Eucitzen/liam/STM32_PCB/Liam_PCB/MCU_POWER.kicad_sch

## KiCad design STM32_PCB/Liam_PCB/MCU_POWER.kicad_sch (2025-02-24)

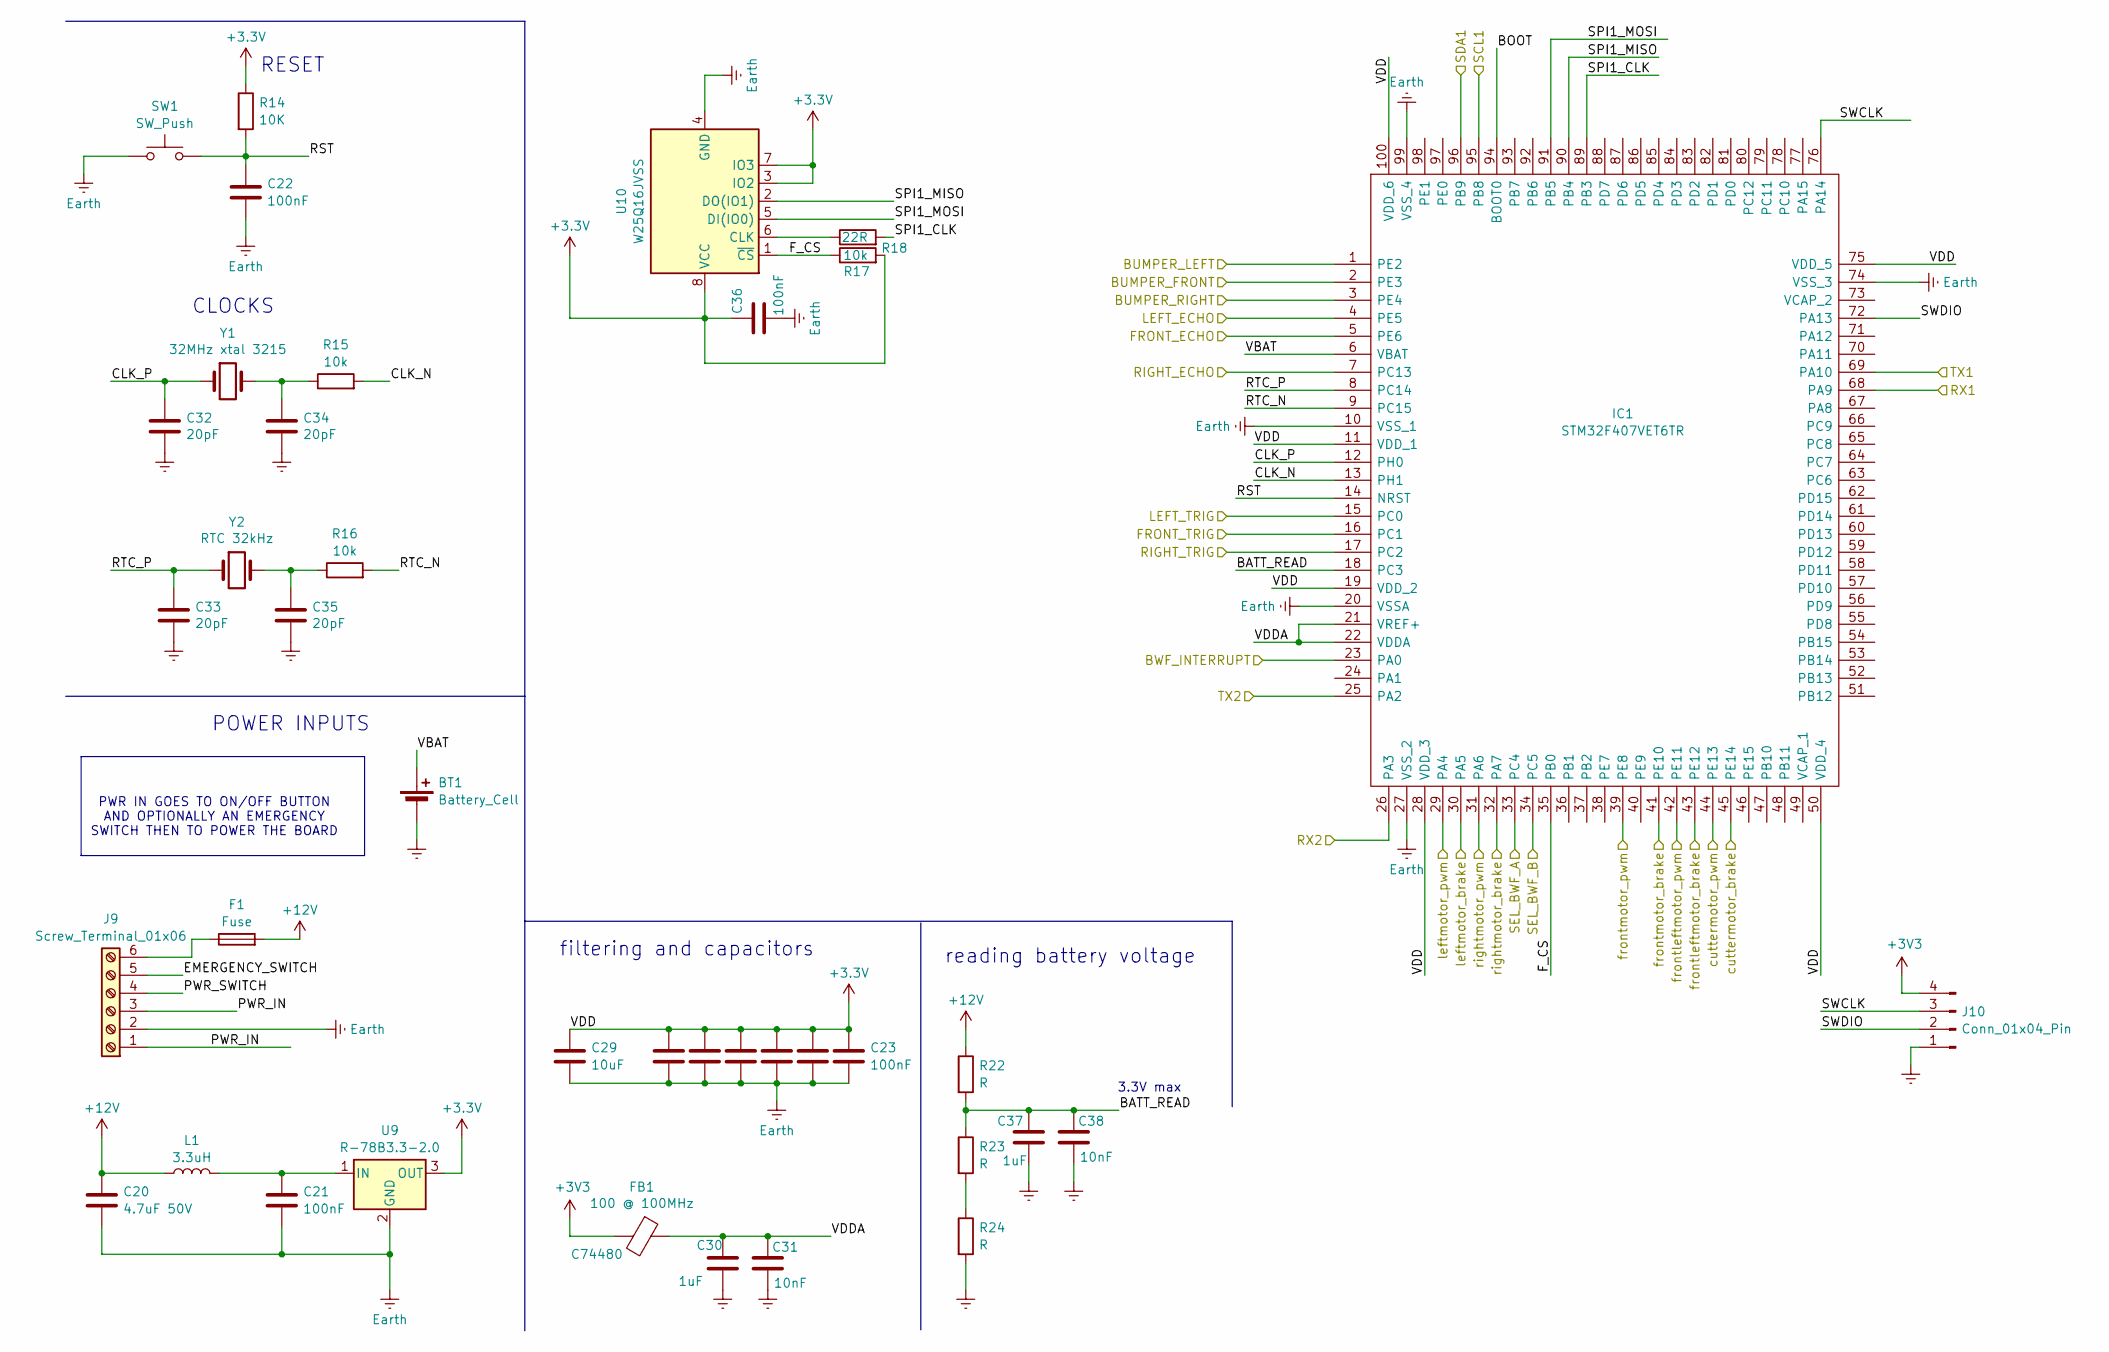
[picture p8: schematic MCU_POWER.kicad_sch]

Parts:
BT1: Battery_Cell
C20: 4.7uF 50V
C21, C22, C23, C24, C25, C26, C27, C28, C36: 100nF
C29: 10uF
C30, C37: 1uF; C_0805_2012Metric_Pad1.15x1.40mm_HandSolder
C31, C38: 10nF; C_0805_2012Metric_Pad1.15x1.40mm_HandSolder
C32, C33, C34, C35: 20pF; C_0805_2012Metric_Pad1.18x1.45mm_HandSolder
F1: Fuse
FB1: 100 @ 100MHz; L_0805_2012Metric_Pad1.15x1.40mm_HandSolder
IC1: STM32F407VET6TR; QFP50P1600X1600X160-100N; Manufacturer_Part_Number STM32F407VET6TR; Mouser Part Number 511-STM32F407VET6TR
J9: Screw_Terminal_01x06
J10: Conn_01x04_Pin
L1: 3.3uH
R14: 10K
R15, R16, R17: 10k
R18: 22R
R22, R23, R24: R
SW1: SW_Push
U9: R-78B3.3-2.0; Converter_DCDC_RECOM_R-78B-2.0_THT
U10: W25Q16JVSS; SOIC-8_5.23x5.23mm_P1.27mm
Y1: 32MHz xtal 3215; Crystal_SMD3215
Y2: RTC 32kHz; Crystal_SMD_HC49-SD_HandSoldering

Connections:
+3.3V: C23.1, C24.1, C25.1, C26.1, C27.1, C28.1, C29.1, C36.1, IC1.11 (VDD_1), IC1.19 (VDD_2), IC1.28 (VDD_3), IC1.50 (VDD_4), IC1.75 (VDD_5), IC1.100 (VDD_6), R14.1, R17.2, U9.3 (OUT), U10.3 (IO2), U10.7 (IO3), U10.8 (VCC)
+3V3: FB1.2, J10.4
+12V: C20.1, F1.2, L1.1, R22.1
BATT_READ: C37.1, C38.1, IC1.18 (PC3), R22.2, R23.1
BOOT: IC1.94 (BOOT0)
BUMPER_FRONT: IC1.2 (PE3)
BUMPER_LEFT: IC1.1 (PE2)
BUMPER_RIGHT: IC1.3 (PE4)
BWF_INTERRUPT: IC1.23 (PA0)
CLK_N: IC1.13 (PH1), R15.2
CLK_P: C32.1, IC1.12 (PH0), Y1.1
EMERGENCY_SWITCH: J9.5
Earth: BT1.2 (-), C20.2, C21.2, C22.2, C23.2, C24.2, C25.2, C26.2, C27.2, C28.2, C29.2, C30.2, C31.2, C32.2, C33.2, C34.2, C35.2, C36.2, C37.2, C38.2, IC1.10 (VSS_1), IC1.20 (VSSA), IC1.27 (VSS_2), IC1.74 (VSS_3), IC1.99 (VSS_4), J9.2, J10.1, R24.2, SW1.1, U9.2 (GND), U10.4 (GND)
FRONT_ECHO: IC1.5 (PE6)
FRONT_TRIG: IC1.16 (PC1)
F_CS: IC1.35 (PB0), R17.1, U10.1 (~CS)
LEFT_ECHO: IC1.4 (PE5)
LEFT_TRIG: IC1.15 (PC0)
unnamed: C21.1, L1.2, U9.1 (IN)
unnamed: C34.1, R15.1, Y1.2
unnamed: C35.1, R16.1, Y2.2
unnamed: F1.1, J9.6
unnamed: R18.1, U10.6 (CLK)
unnamed: R23.2, R24.1
PWR_IN: J9.1, J9.3
PWR_SWITCH: J9.4
RIGHT_ECHO: IC1.7 (PC13)
RIGHT_TRIG: IC1.17 (PC2)
RST: C22.1, IC1.14 (NRST), R14.2, SW1.2
RTC_N: IC1.9 (PC15), R16.2
RTC_P: C33.1, IC1.8 (PC14), Y2.1
RX1: IC1.68 (PA9)
RX2: IC1.26 (PA3)
SCL1: IC1.95 (PB8)
SDA1: IC1.96 (PB9)
SEL_BWF_A: IC1.33 (PC4)
SEL_BWF_B: IC1.34 (PC5)
SPI1_CLK: IC1.89 (PB3), R18.2
SPI1_MISO: IC1.90 (PB4), U10.2 (DO(IO1))
SPI1_MOSI: IC1.91 (PB5), U10.5 (DI(IO0))
SWCLK: IC1.76 (PA14), J10.3
SWDIO: IC1.72 (PA13), J10.2
TX1: IC1.69 (PA10)
TX2: IC1.25 (PA2)
VBAT: BT1.1 (+), IC1.6 (VBAT)
VDDA: C30.1, C31.1, FB1.1, IC1.21 (VREF+), IC1.22 (VDDA)
cuttermotor_brake: IC1.45 (PE14)
cuttermotor_pwm: IC1.44 (PE13)
frontleftmotor_brake: IC1.43 (PE12)
frontleftmotor_pwm: IC1.42 (PE11)
frontmotor_brake: IC1.41 (PE10)
frontmotor_pwm: IC1.39 (PE8)
leftmotor_brake: IC1.30 (PA5)
leftmotor_pwm: IC1.29 (PA4)
rightmotor_brake: IC1.32 (PA7)
rightmotor_pwm: IC1.31 (PA6)

Notes on the sheet:
CLOCKS
PWR IN GOES TO ON/OFF BUTTON AND OPTIONALLY AN EMERGENCY SWITCH THEN TO POWER THE BOARD
RESET
reading battery voltage
filtering and capacitors
POWER INPUTS
3.3V max
