Eucitzen/liam/STM32_PCB/Liam_PCB/motor.kicad_sch

## KiCad design STM32_PCB/Liam_PCB/motor.kicad_sch (2025-02-24)

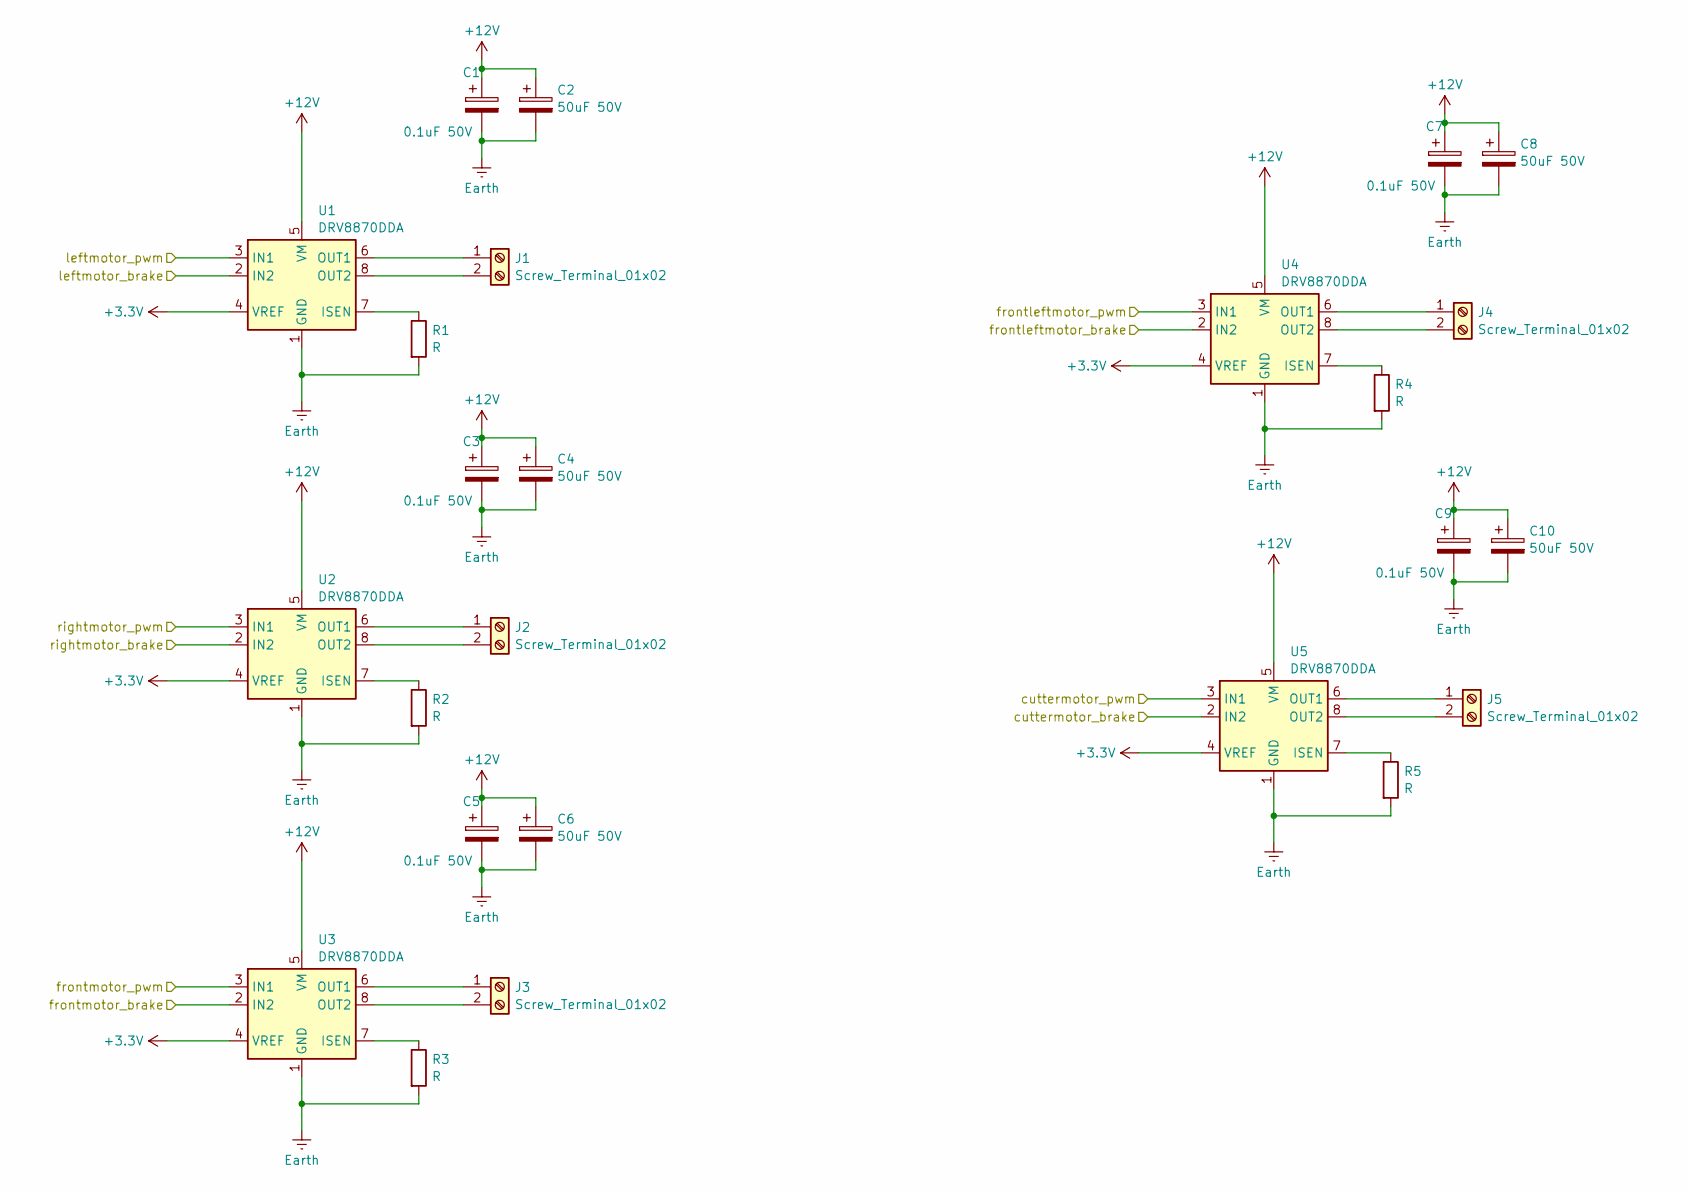
[picture p9: schematic motor.kicad_sch]

Parts:
C1, C3, C5, C7, C9: 0.1uF 50V
C2, C4, C6, C8, C10: 50uF 50V
J1, J2, J3, J4, J5: Screw_Terminal_01x02
R1, R2, R3, R4, R5: R
U1, U2, U3, U4, U5: DRV8870DDA; Texas_HTSOP-8-1EP_3.9x4.9mm_P1.27mm_EP2.95x4.9mm_Mask2.4x3.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

Connections:
+3.3V: U1.4 (VREF), U2.4 (VREF), U3.4 (VREF), U4.4 (VREF), U5.4 (VREF)
+12V: C1.1, C2.1, C3.1, C4.1, C5.1, C6.1, C7.1, C8.1, C9.1, C10.1, U1.5 (VM), U2.5 (VM), U3.5 (VM), U4.5 (VM), U5.5 (VM)
Earth: C1.2, C2.2, C3.2, C4.2, C5.2, C6.2, C7.2, C8.2, C9.2, C10.2, R1.2, R2.2, R3.2, R4.2, R5.2, U1.1 (GND), U1.9 (GND), U2.1 (GND), U2.9 (GND), U3.1 (GND), U3.9 (GND), U4.1 (GND), U4.9 (GND), U5.1 (GND), U5.9 (GND)
unnamed: J1.1, U1.6 (OUT1)
unnamed: J1.2, U1.8 (OUT2)
unnamed: J2.1, U2.6 (OUT1)
unnamed: J2.2, U2.8 (OUT2)
unnamed: J3.1, U3.6 (OUT1)
unnamed: J3.2, U3.8 (OUT2)
unnamed: J4.1, U4.6 (OUT1)
unnamed: J4.2, U4.8 (OUT2)
unnamed: J5.1, U5.6 (OUT1)
unnamed: J5.2, U5.8 (OUT2)
unnamed: R1.1, U1.7 (ISEN)
unnamed: R2.1, U2.7 (ISEN)
unnamed: R3.1, U3.7 (ISEN)
unnamed: R4.1, U4.7 (ISEN)
unnamed: R5.1, U5.7 (ISEN)
cuttermotor_brake: U5.2 (IN2)
cuttermotor_pwm: U5.3 (IN1)
frontleftmotor_brake: U4.2 (IN2)
frontleftmotor_pwm: U4.3 (IN1)
frontmotor_brake: U3.2 (IN2)
frontmotor_pwm: U3.3 (IN1)
leftmotor_brake: U1.2 (IN2)
leftmotor_pwm: U1.3 (IN1)
rightmotor_brake: U2.2 (IN2)
rightmotor_pwm: U2.3 (IN1)
