Eucitzen/liam/STM32_PCB/Liam_PCB/untitled.kicad_sch

## KiCad design STM32_PCB/Liam_PCB/untitled.kicad_sch (2025-02-24)

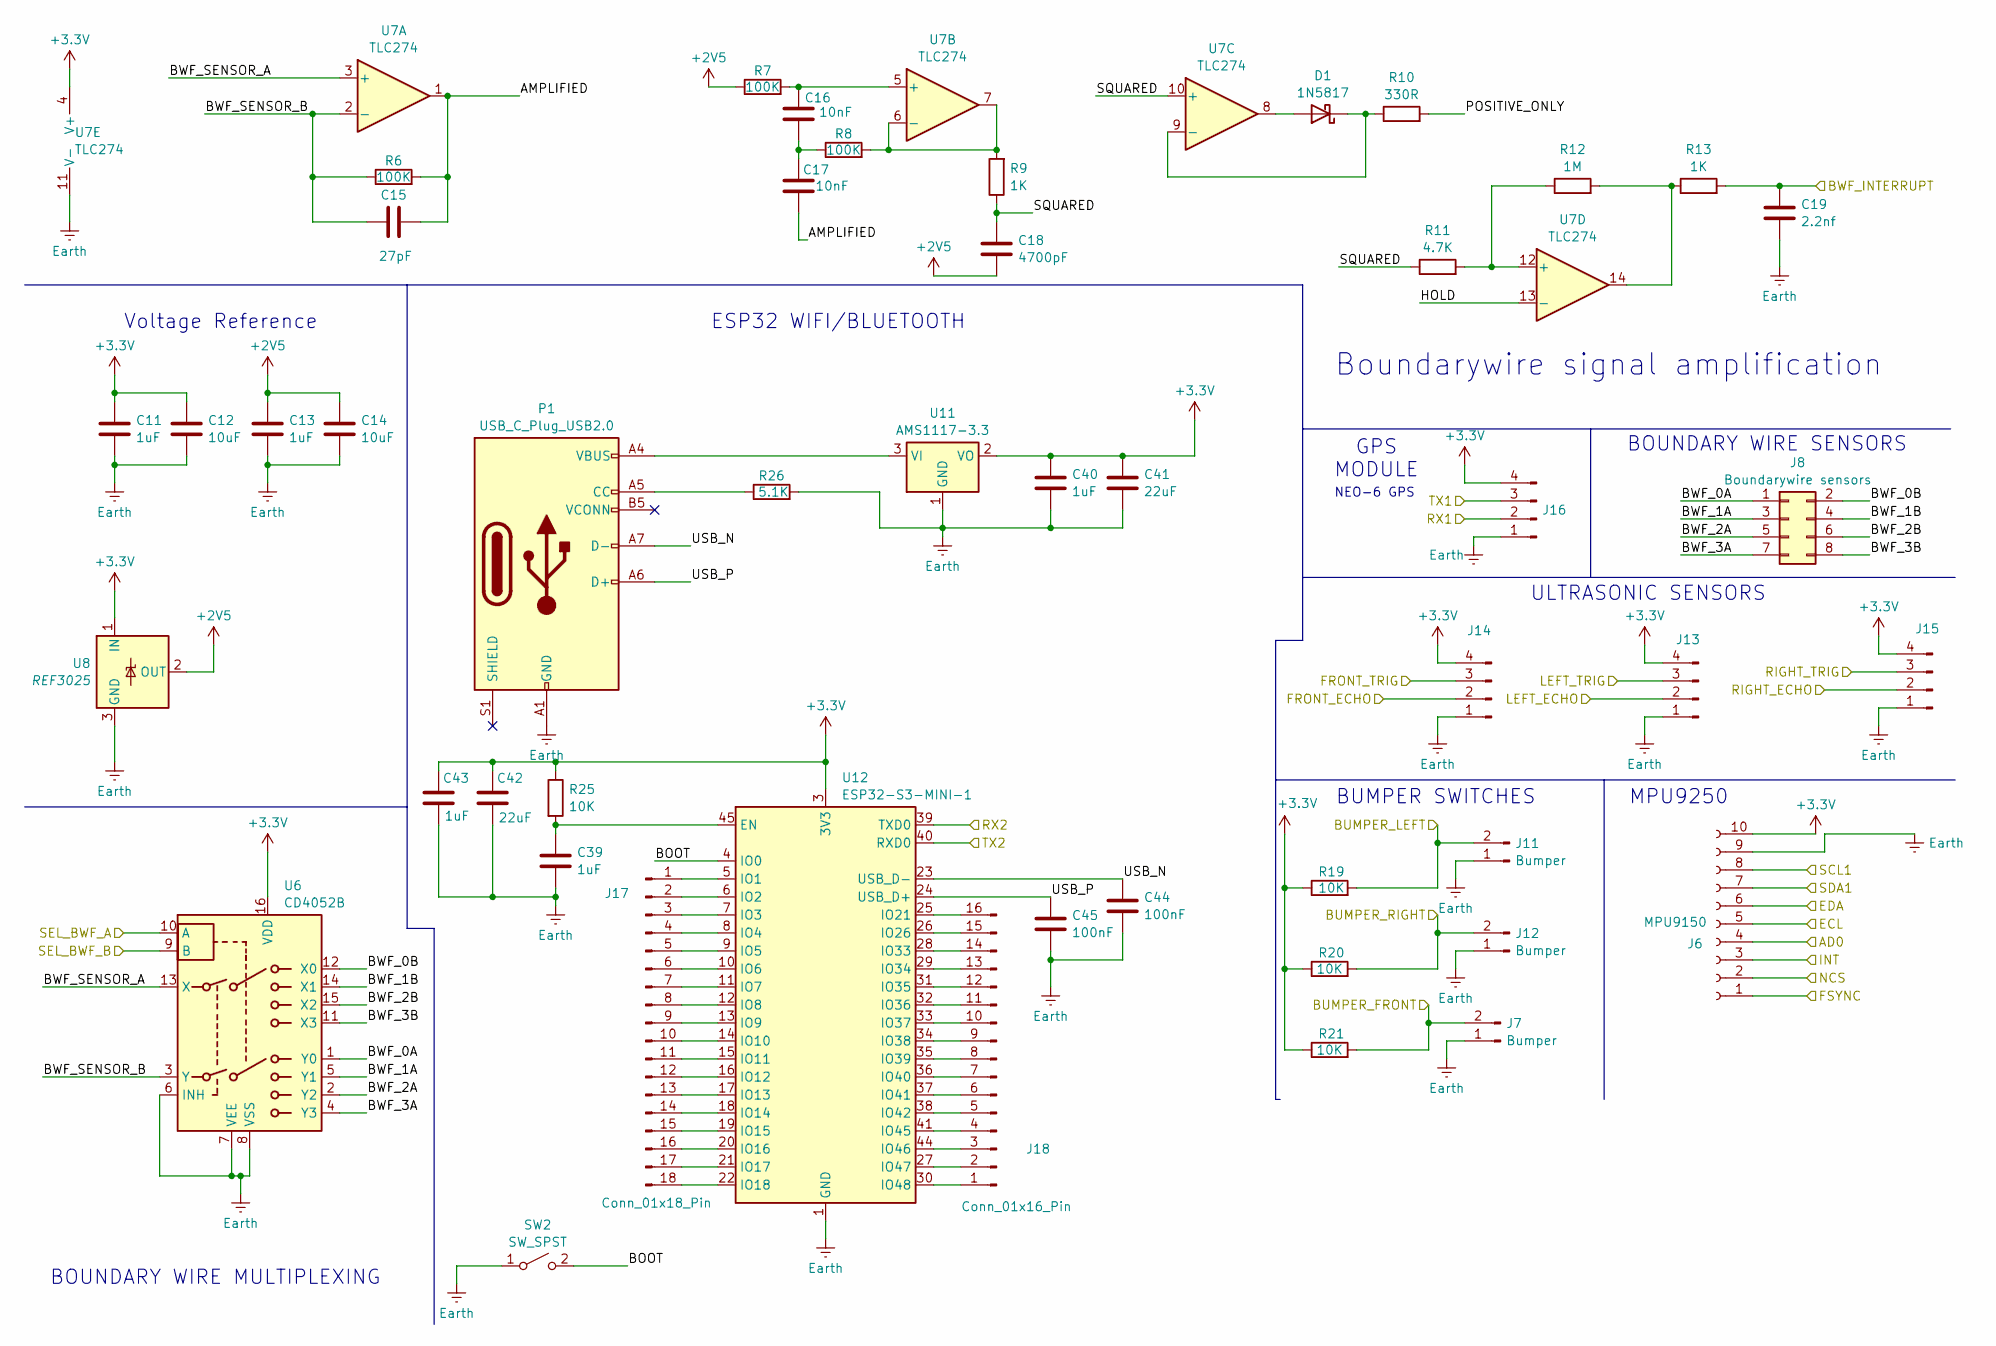
[picture p10: schematic untitled.kicad_sch]

Parts:
C11, C13, C39, C40, C43: 1uF
C12, C14: 10uF
C15: 27pF
C16, C17: 10nF
C18: 4700pF
C19: 2.2nf
C41, C42: 22uF
C44, C45: 100nF
D1: 1N5817; D_DO-41_SOD81_P10.16mm_Horizontal
J6: MPU9150
J7, J11, J12: Bumper
J8: Boundarywire sensors
J13, J14, J15, J16: Conn_01x04_Pin
J17: Conn_01x18_Pin
J18: Conn_01x16_Pin
P1: USB_C_Plug_USB2.0
R6, R7, R8: 100K
R9, R13: 1K
R10: 330R
R11: 4.7K
R12: 1M
R19, R20, R21, R25: 10K
R26: 5.1K
SW2: SW_SPST
U6: CD4052B
U7: TLC274
U8: REF3025; SOT-23
U11: AMS1117-3.3; SOT-223-3_TabPin2
U12: ESP32-S3-MINI-1; ESP32-S2-MINI-1

Connections:
+2V5: C13.1, C14.1, C18.2, R7.1, U8.2 (OUT)
+3.3V: C11.1, C12.1, C40.1, C41.1, C42.1, C43.1, J6.10, J13.4, J14.4, J15.4, J16.4, R19.1, R20.1, R21.1, R25.1, U6.16 (VDD), U7.4 (V+), U8.1 (IN), U11.2 (VO), U12.3 (3V3)
AD0: J6.4
AMPLIFIED: C15.2, C17.2, R6.2, U7.1
BOOT: SW2.2 (B), U12.4 (IO0)
BUMPER_FRONT: J7.2, R21.2
BUMPER_LEFT: J11.2, R19.2
BUMPER_RIGHT: J12.2, R20.2
BWF_0A: J8.1, U6.1 (Y0)
BWF_0B: J8.2, U6.12 (X0)
BWF_1A: J8.3, U6.5 (Y1)
BWF_1B: J8.4, U6.14 (X1)
BWF_2A: J8.5, U6.2 (Y2)
BWF_2B: J8.6, U6.15 (X2)
BWF_3A: J8.7, U6.4 (Y3)
BWF_3B: J8.8, U6.11 (X3)
BWF_INTERRUPT: C19.1, R13.2
BWF_SENSOR_A: U6.13 (X), U7.3 (+)
BWF_SENSOR_B: C15.1, R6.1, U6.3 (Y), U7.2 (-)
ECL: J6.5
EDA: J6.6
Earth: C11.2, C12.2, C13.2, C14.2, C19.2, C39.2, C40.2, C41.2, C42.2, C43.2, C44.2, C45.2, J6.9, J7.1, J11.1, J12.1, J13.1, J14.1, J15.1, J16.1, P1.A1 (GND), P1.A12 (GND), P1.B1 (GND), P1.B12 (GND), R26.2, SW2.1 (A), U6.6 (INH), U6.7 (VEE), U6.8 (VSS), U7.11 (V-), U8.3 (GND), U11.1 (GND), U12.1 (GND), U12.2 (GND), U12.42 (GND), U12.43 (GND), U12.46 (GND), U12.47 (GND), U12.48 (GND), U12.49 (GND), U12.50 (GND), U12.51 (GND), U12.52 (GND), U12.53 (GND), U12.54 (GND), U12.55 (GND), U12.56 (GND), U12.57 (GND), U12.58 (GND), U12.59 (GND), U12.60 (GND), U12.61 (GND), U12.62 (GND), U12.63 (GND), U12.64 (GND), U12.65 (GND)
FRONT_ECHO: J14.2
FRONT_TRIG: J14.3
FSYNC: J6.1
HOLD: U7.13 (-)
INT: J6.3
LEFT_ECHO: J13.2
LEFT_TRIG: J13.3
NCS: J6.2
unnamed: C16.1, R7.2, U7.5 (+)
unnamed: C16.2, C17.1, R8.1
unnamed: C39.1, R25.2, U12.45 (EN)
unnamed: D1.1 (K), R10.1, U7.9 (-)
unnamed: D1.2 (A), U7.8
unnamed: J17.1, U12.5 (IO1)
unnamed: J17.2, U12.6 (IO2)
unnamed: J17.3, U12.7 (IO3)
unnamed: J17.4, U12.8 (IO4)
unnamed: J17.5, U12.9 (IO5)
unnamed: J17.6, U12.10 (IO6)
unnamed: J17.7, U12.11 (IO7)
unnamed: J17.8, U12.12 (IO8)
unnamed: J17.9, U12.13 (IO9)
unnamed: J17.10, U12.14 (IO10)
unnamed: J17.11, U12.15 (IO11)
unnamed: J17.12, U12.16 (IO12)
unnamed: J17.13, U12.17 (IO13)
unnamed: J17.14, U12.18 (IO14)
unnamed: J17.15, U12.19 (IO15)
unnamed: J17.16, U12.20 (IO16)
unnamed: J17.17, U12.21 (IO17)
unnamed: J17.18, U12.22 (IO18)
unnamed: J18.1, U12.30 (IO48)
unnamed: J18.2, U12.27 (IO47)
unnamed: J18.3, U12.44 (IO46)
unnamed: J18.4, U12.41 (IO45)
unnamed: J18.5, U12.38 (IO42)
unnamed: J18.6, U12.37 (IO41)
unnamed: J18.7, U12.36 (IO40)
unnamed: J18.8, U12.35 (IO39)
unnamed: J18.9, U12.34 (IO38)
unnamed: J18.10, U12.33 (IO37)
unnamed: J18.11, U12.32 (IO36)
unnamed: J18.12, U12.31 (IO35)
unnamed: J18.13, U12.29 (IO34)
unnamed: J18.14, U12.28 (IO33)
unnamed: J18.15, U12.26 (IO26)
unnamed: J18.16, U12.25 (IO21)
unnamed: P1.A4 (VBUS), P1.A9 (VBUS), P1.B4 (VBUS), P1.B9 (VBUS), U11.3 (VI)
unnamed: P1.A5 (CC), R26.1
unnamed: R8.2, R9.2, U7.6 (-), U7.7
unnamed: R11.2, R12.1, U7.12 (+)
unnamed: R12.2, R13.1, U7.14
POSITIVE_ONLY: R10.2
RIGHT_ECHO: J15.2
RIGHT_TRIG: J15.3
RX1: J16.2
RX2: U12.39 (TXD0)
SCL1: J6.8
SDA1: J6.7
SEL_BWF_A: U6.10 (A)
SEL_BWF_B: U6.9 (B)
SQUARED: C18.1, R9.1, R11.1, U7.10 (+)
TX1: J16.3
TX2: U12.40 (RXD0)
USB_N: C44.1, P1.A7 (D-), U12.23 (USB_D-)
USB_P: C45.1, P1.A6 (D+), U12.24 (USB_D+)

Notes on the sheet:
ESP32 WIFI/BLUETOOTH
MPU9250
BOUNDARY WIRE SENSORS
Boundarywire signal amplification
Voltage Reference
BOUNDARY WIRE MULTIPLEXING
NEO-6 GPS
BUMPER SWITCHES
GPS MODULE
ULTRASONIC SENSORS
